sdrum01/DUB-IY/CAD/DXF/Front_DUBIY_mit_Beschriftung_buisnesscard.jpg

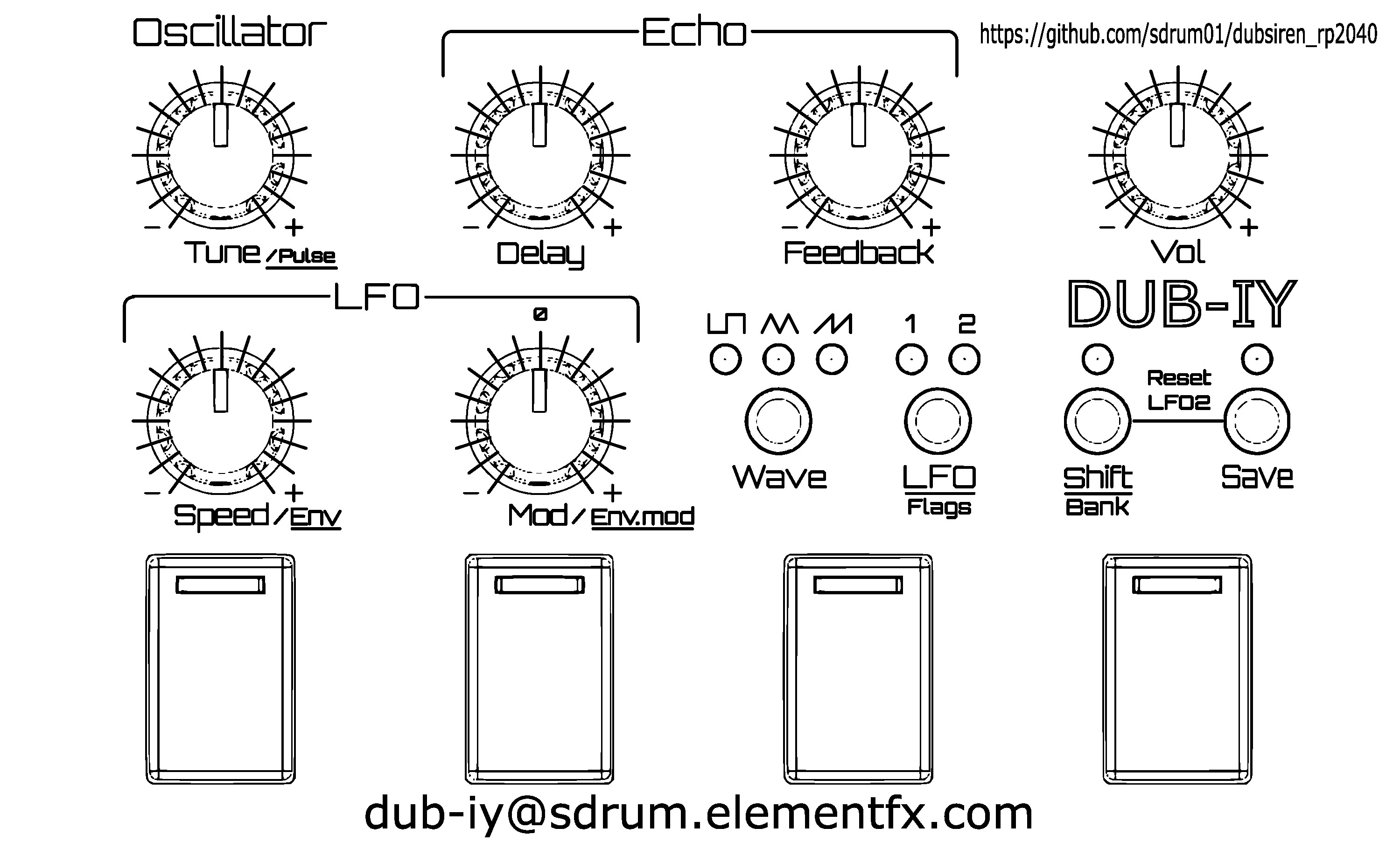
CAD/DXF/Front_DUBIY_mit_Beschriftung_buisnesscard.jpg
