sdrum01/DUB-IY/CAD/STL/11/DIYDeckel_V11.4_5mm.stl

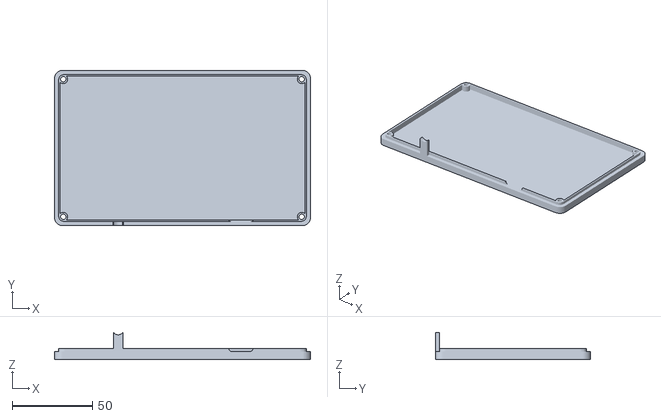
[picture p22: CAD file, 2026-10-09]
CAD/STL/11/DIYDeckel_V11.4_5mm.stl
160.0 x 97.0 x 17.0
