sdrum01/DUB-IY/CAD/STL/12/DIYBodyBottomSlim_V12.3.stl

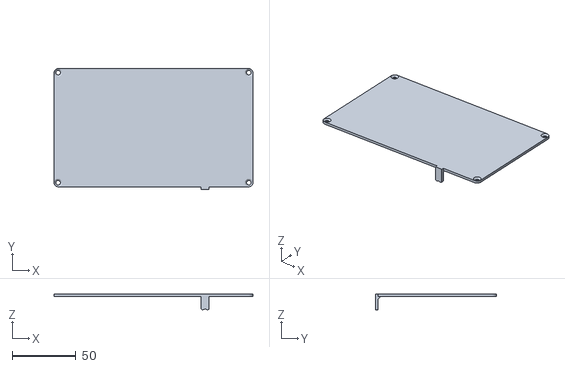
[picture p23: CAD file, 2026-10-09]
CAD/STL/12/DIYBodyBottomSlim_V12.3.stl
155.5 x 94.5 x 12.3
