sdrum01/DUB-IY/CAD/DXF/DIYBody - Frontplatte_EMS_grosse_schrift.dxf

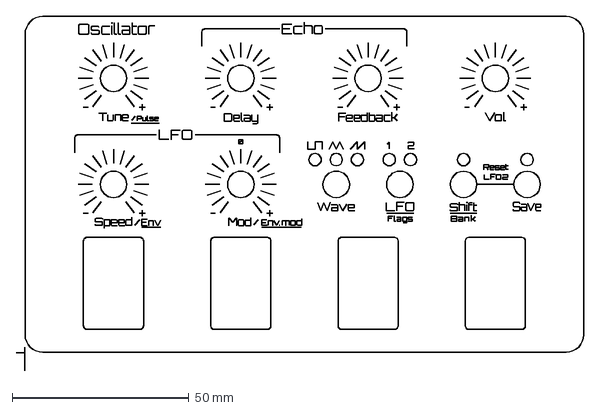
[picture p24: CAD file, 2026-10-09]
CAD/DXF/DIYBody - Frontplatte_EMS_grosse_schrift.dxf
160.5 x 100.2 mm
