sdrum01/DUB-IY/CAD/STL/10/DIYStreifen_V10.1.stl

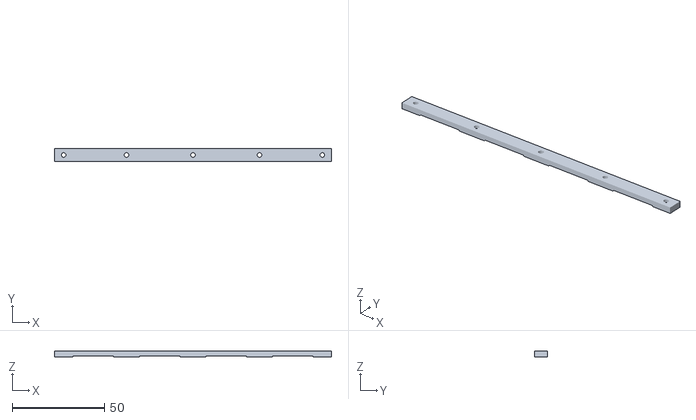
[picture p25: CAD file, 2026-10-09]
CAD/STL/10/DIYStreifen_V10.1.stl
150.0 x 7.00 x 3.00
