sdrum01/DUB-IY/CAD/STL/11/PotiKnob_inlay_V11.6.stl

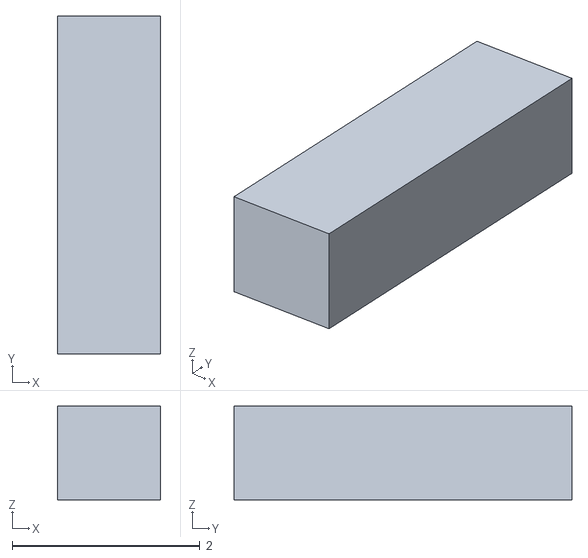
[picture p26: CAD file, 2026-10-09]
CAD/STL/11/PotiKnob_inlay_V11.6.stl
1.10 x 3.60 x 1.00
