sdrum01/DUB-IY/CAD/STL/10/DIYBody_V10.2.stl

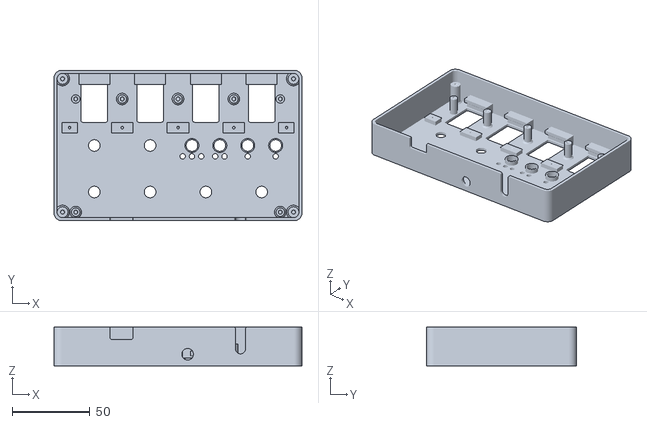
[picture p27: CAD file, 2026-10-09]
CAD/STL/10/DIYBody_V10.2.stl
160.0 x 97.0 x 25.0
