sdrum01/DUB-IY/CAD/STL/11/PotiKnob_V11.6.stl

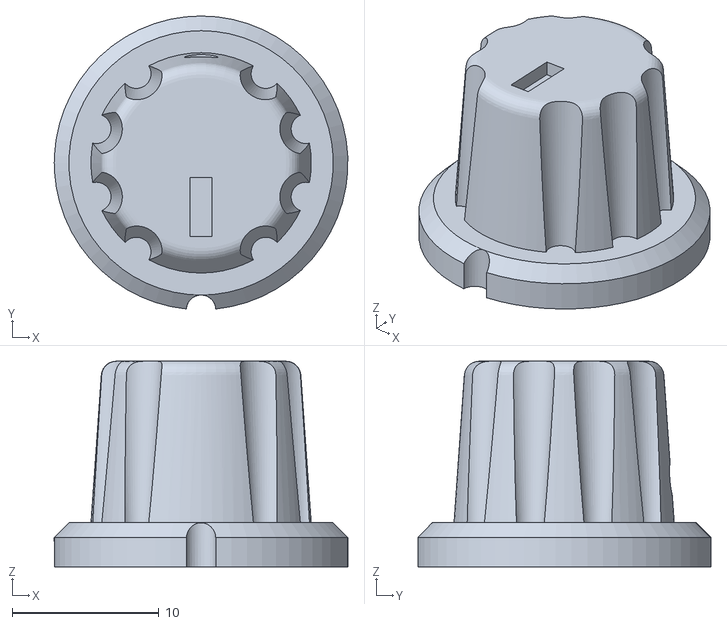
[picture p28: CAD file, 2026-10-09]
CAD/STL/11/PotiKnob_V11.6.stl
20.0 x 19.9 x 14.0
