sdrum01/DUB-IY/CAD/STL/11/DIYKnobFireInlaysquare_V11.1.stl

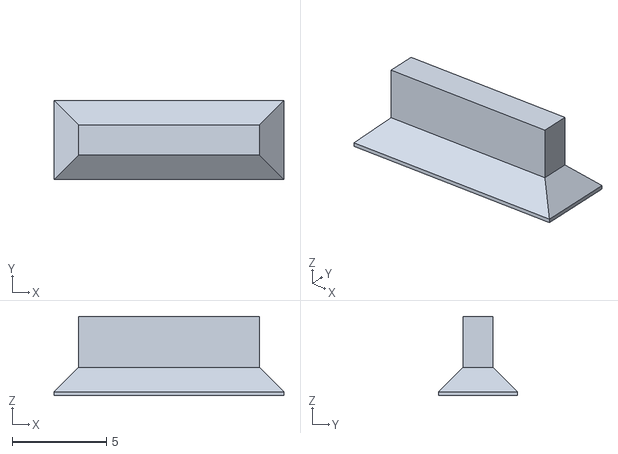
[picture p29: CAD file, 2026-10-09]
CAD/STL/11/DIYKnobFireInlaysquare_V11.1.stl
12.2 x 4.20 x 4.20
