sdrum01/DUB-IY/CAD/STL/11/DIYBody - Rahmen.stl

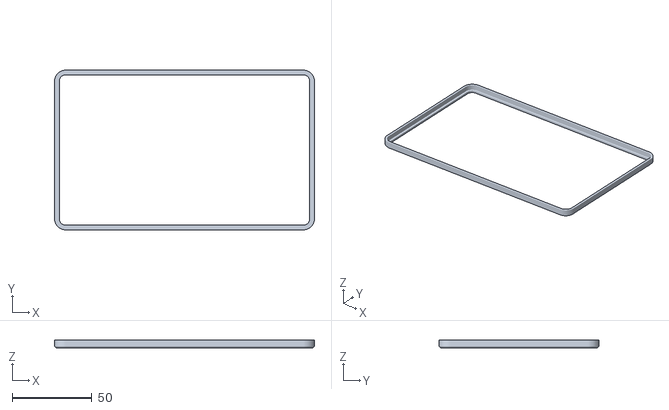
[picture p30: CAD file, 2026-10-09]
CAD/STL/11/DIYBody - Rahmen.stl
163.4 x 100.4 x 5.00
