sdrum01/DUB-IY/CAD/STL/12/DIYKnobFire - Stößel_V12.3_1.stl

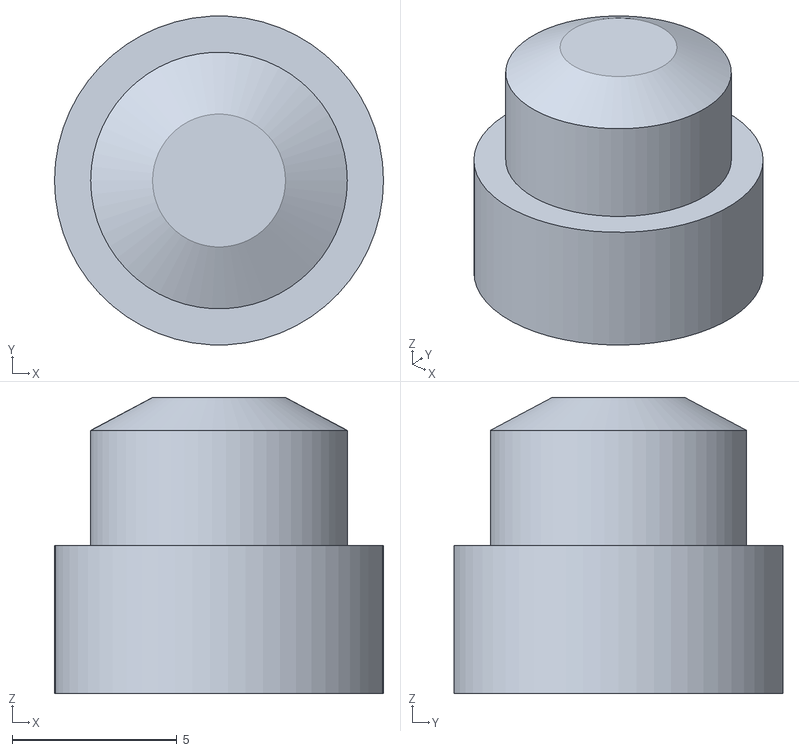
[picture p31: CAD file, 2026-10-09]
CAD/STL/12/DIYKnobFire - Stößel_V12.3_1.stl
10.0 x 9.99 x 9.00
