sdrum01/DUB-IY/CAD/STL/11/DIYDeckel_V11.4_15mm.stl

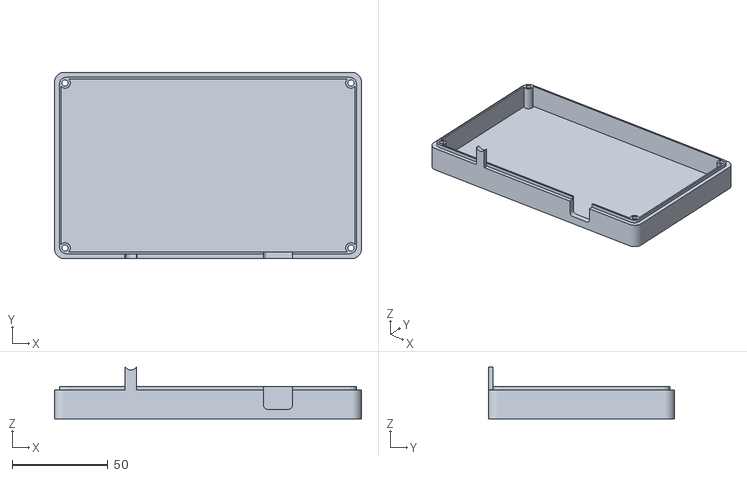
[picture p32: CAD file, 2026-10-09]
CAD/STL/11/DIYDeckel_V11.4_15mm.stl
160.0 x 97.0 x 27.0
