sdrum01/DUB-IY/CAD/STL/12/PotiKnob - Inlays_x10_V12.0.stl

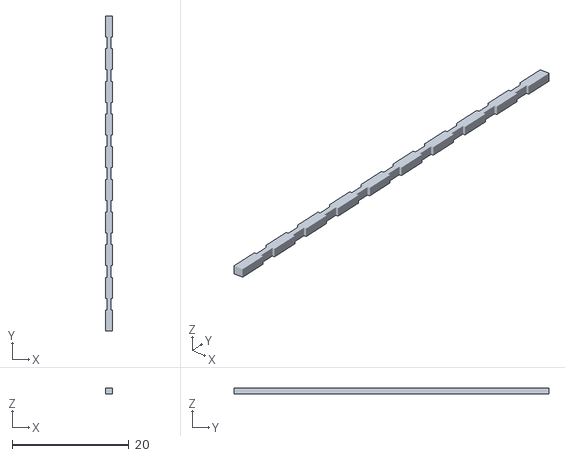
[picture p33: CAD file, 2026-10-09]
CAD/STL/12/PotiKnob - Inlays_x10_V12.0.stl
1.20 x 54.0 x 1.00
