sdrum01/DUB-IY/CAD/STL/11/DIYDeckel_V11.1_10mm.stl

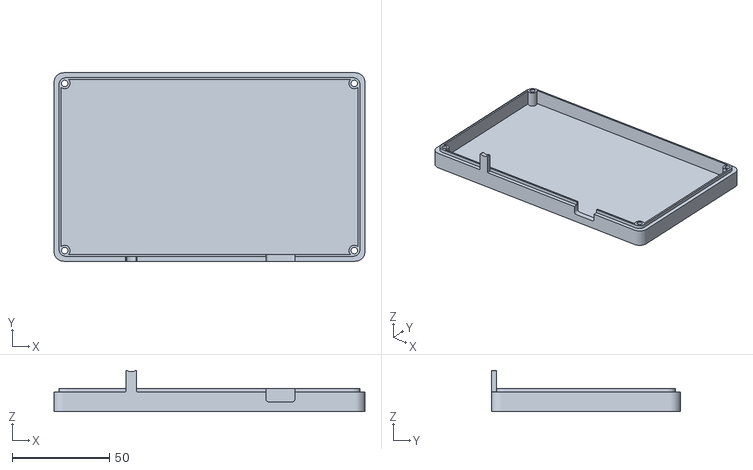
[picture p34: CAD file, 2026-10-09]
CAD/STL/11/DIYDeckel_V11.1_10mm.stl
160.0 x 97.0 x 21.2
