sdrum01/DUB-IY/CAD/STL/12/DIYBody_V12.3.stl

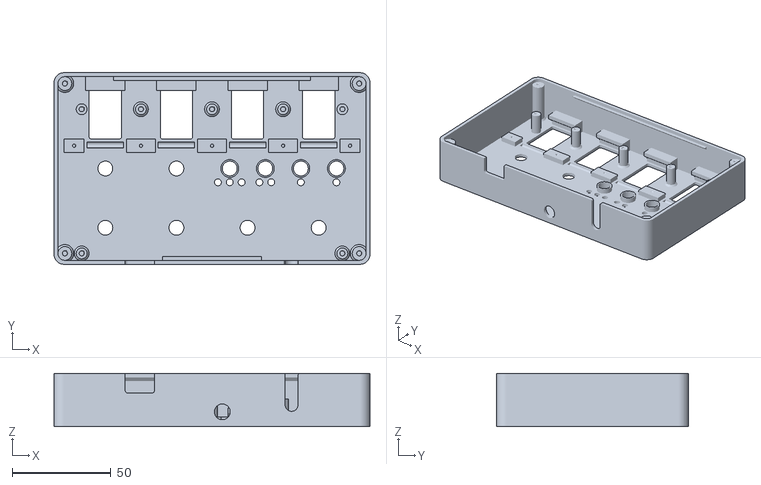
[picture p35: CAD file, 2026-10-09]
CAD/STL/12/DIYBody_V12.3.stl
160.0 x 97.0 x 27.0
